IronZack95/Polimi_Board/Datasheets/0693W000003Bg2XQAS.png

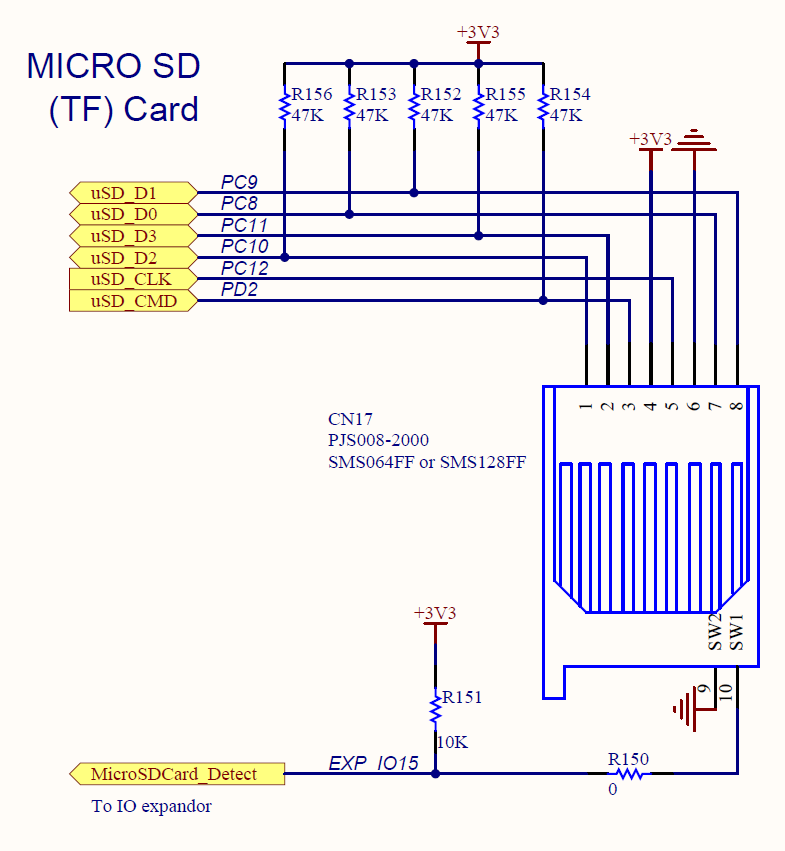
Datasheets/0693W000003Bg2XQAS.png
