IronZack95/Polimi_Board/Datasheets/two rs232.jpg

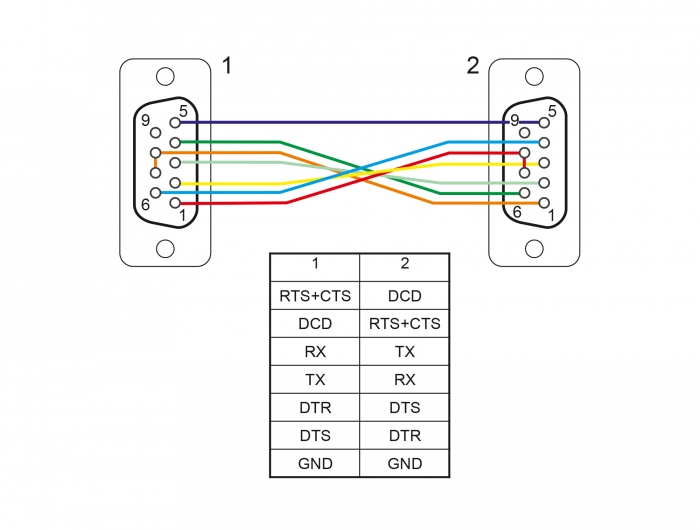
Datasheets/two rs232.jpg
