IronZack95/Polimi_Board/Render2/Screenshot 2025-08-23 141944.png

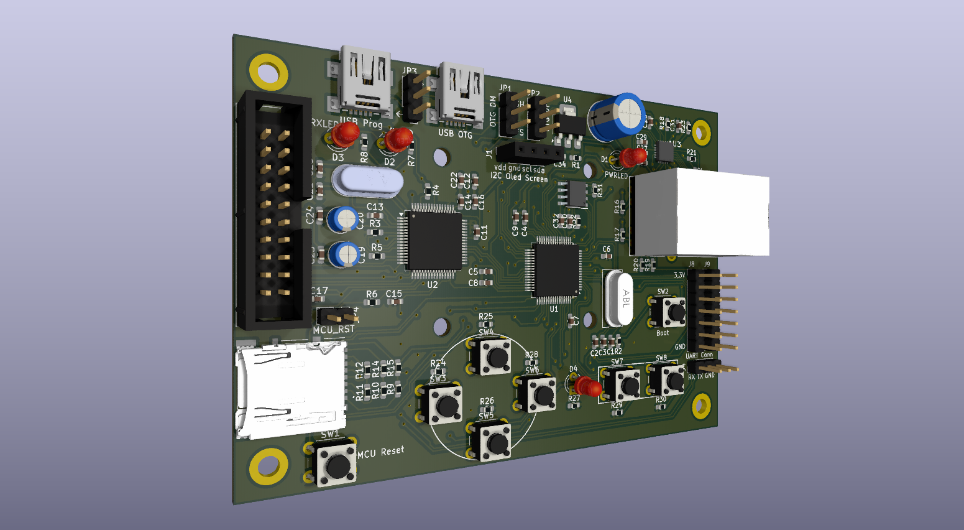
Render2/Screenshot 2025-08-23 141944.png
