IronZack95/Polimi_Board/Render/back zoom raytracing.png

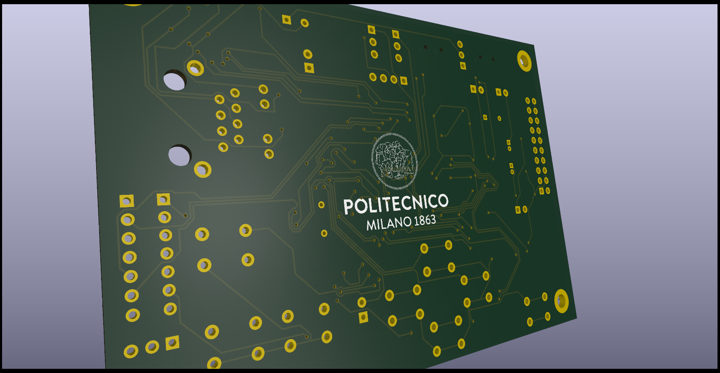
Render/back zoom raytracing.png
