IronZack95/Polimi_Board/Render/Polimi Board Front.png

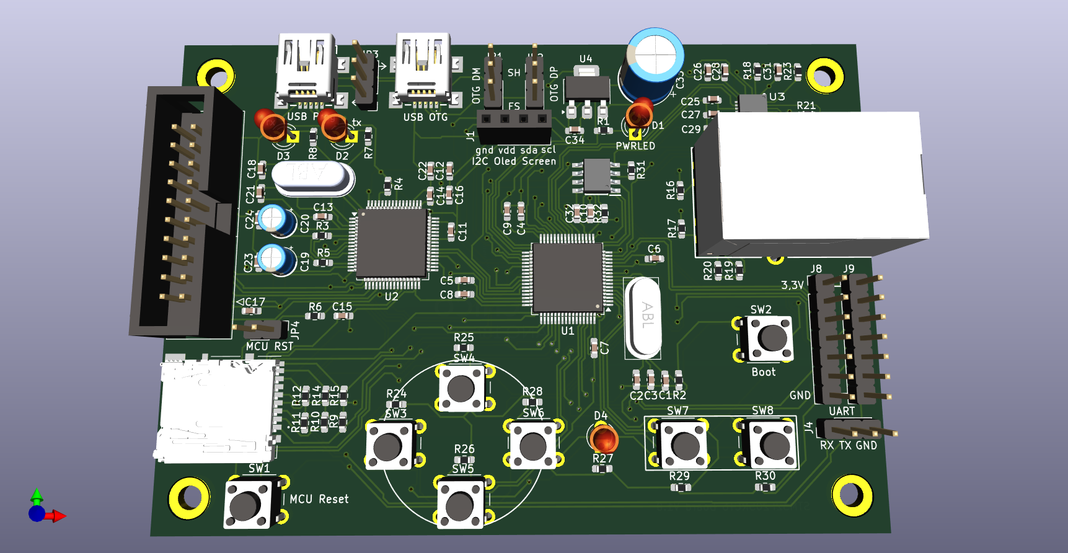
Render/Polimi Board Front.png
