IronZack95/Polimi_Board/Render/Polimi Board Front_no comp.png

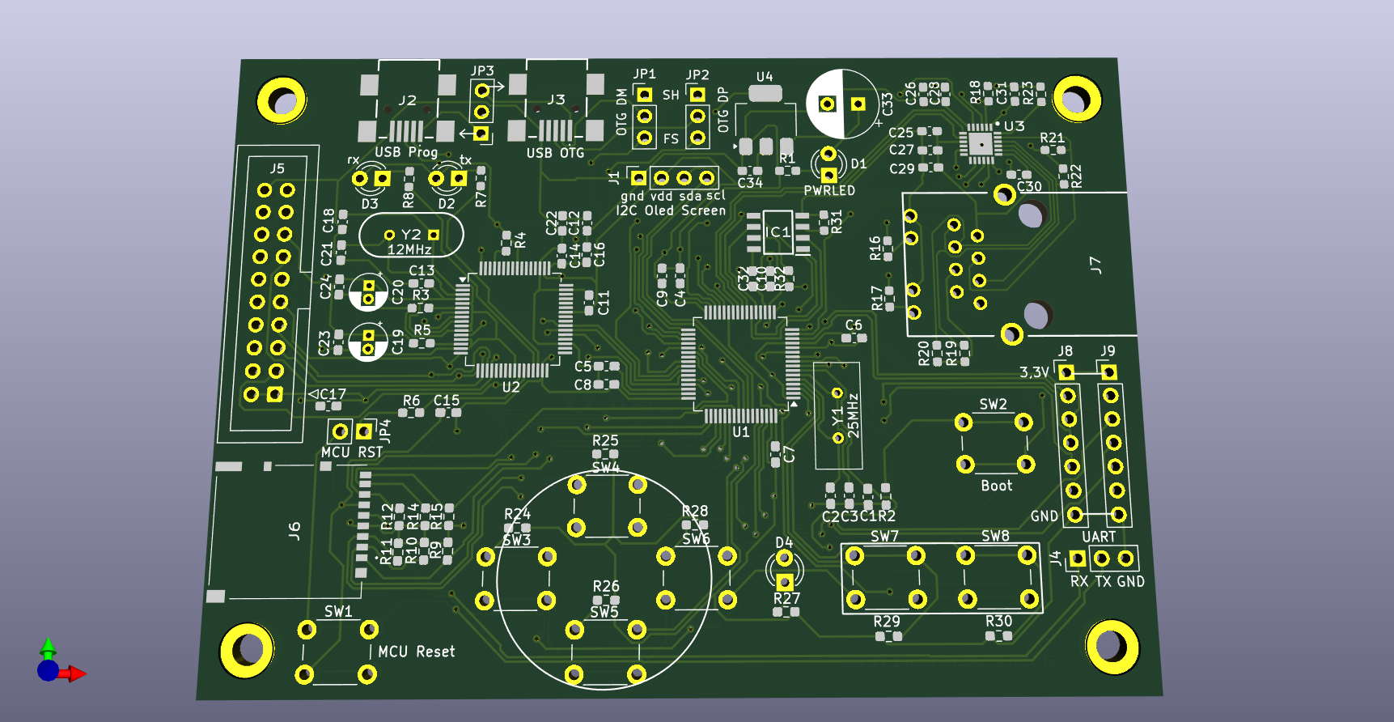
Render/Polimi Board Front_no comp.png
